chanulee/cote/appendix/visionOscDatapoints/1face.png

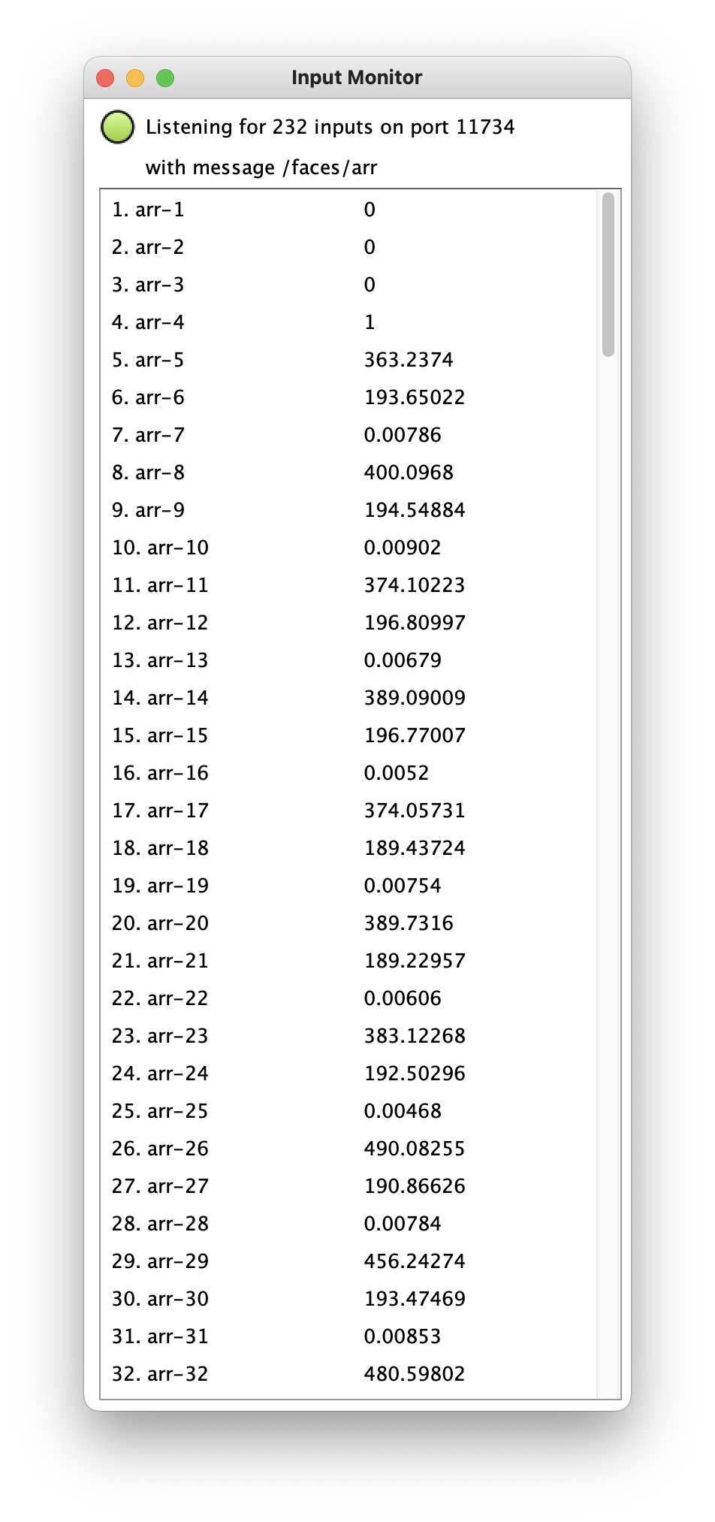
appendix/visionOscDatapoints/1face.png
