chanulee/cote/testcode/keypressedSerial/src/main.cpp

#include "ofMain.h"
#include "ofApp.h"

//========================================================================
int main( ){

	//Use ofGLFWWindowSettings for more options like multi-monitor fullscreen
	ofGLWindowSettings settings;
	settings.setSize(255, 255);
	settings.windowMode = OF_WINDOW; //can also be OF_FULLSCREEN

	auto window = ofCreateWindow(settings);

	ofRunApp(window, make_shared<ofApp>());
	ofRunMainLoop();

}
